pschilkdev/QuadCopter_PP/PPQCU_RC_REMOTE.X/config.h

/* 
 * File:   config.h
 * Author: Philipp
 *
 * Created on January 2, 2016, 3:40 AM
 */

#ifndef CONFIG_H
#define	CONFIG_H

#ifdef	__cplusplus
extern "C" {
#endif

#include <xc.h>



#ifdef	__cplusplus
}
#endif

#endif	/* CONFIG_H */
