pschilkdev/QuadCopter_PP/PPQCU_CU_MAIN.X/NRF.h

/* 
 * File:   NRF.h
 * Author: Philipp
 *
 * Created on January 2, 2016, 6:30 PM
 */

#ifndef NRF_H
#define	NRF_H

#ifdef	__cplusplus
extern "C" {
#endif
    
#include "SPI.h"
#include "config.h"
#include <xc.h>
#include "IO.h"

// ====== Commands ========
    
#define NRF_CMD__R_REGISTER 0b00000000
#define NRF_CMD__W_REGISTER 0b00100000
#define NRF_CMD__R_RX_PAYLOAD 0b01100000
#define NRF_CMD__W_TX_PAYLOAD 0b10100000
#define NRF_CMD__FLUSH_TX 0b11100001
#define NRF_CMD__FLUSH_RX 0b11100010
#define NRF_CMD__REUSE_TX_PL 0b11100011
#define NRF_CMD__ACTIVATE 0b01010000
#define NRF_CMD__R_RX_PL_WID 0b01100000
#define NRF_CMD__W_ACK_PAYLOAD 0b10101000
#define NRF_CMD__W_TX_PAYLOAD_NO_ACK 0b10110000
#define NRF_CMD__NOP 0b11111111
    
// ====== Registers =======
    
#define NRF_RG__CONFIG 0x00
#define NRF_RG__EN_AA 0x01
#define NRF_RG__EN_RXADDR 0x02
#define NRF_RG__SETUP_AW 0x03
#define NRF_RG__SETUP_RETR 0x04
#define NRF_RG__RF_CH 0x05
#define NRF_RG__RF_SETUP 0x06
#define NRF_RG__STATUS 0x07
#define NRF_RG__OBSERVE_TX 0x08
#define NRF_RG__CD 0x09
#define NRF_RG__RX_ADDR_P0 0x0A
#define NRF_RG__RX_ADDR_P1 0x0B
#define NRF_RG__RX_ADDR_P2 0x0C
#define NRF_RG__RX_ADDR_P3 0x0D
#define NRF_RG__RX_ADDR_P4 0x0E
#define NRF_RG__RX_ADDR_P5 0x0F
#define NRF_RG__TX_ADDR 0x10
#define NRF_RG__RX_PW_P0 0x11
#define NRF_RG__RX_PW_P1 0x12
#define NRF_RG__RX_PW_P2 0x13
#define NRF_RG__RX_PW_P3 0x14
#define NRF_RG__RX_PW_P4 0x15
#define NRF_RG__RX_PW_P5 0x16
#define NRF_RG__FIFO_STATUS 0x17
#define NRF_RG__DYNPD 0x1C
#define NRF_RG__FEATURE 0x1D
    
    void NRF_init(SPI_CHANNEL channel);
    int NRF_cmd(char cmd);
    void NRF_wreg(char Reg,char val);
    int  NRF_rreg(char Reg);
    BOOL NRF_check();
    int NRF_RXBuffer_Length();
    int NRF_RXBuffer(char*);
    void NRF_TXBuffer(char, char*,BOOL);
    
//Values
#define byte3 0b01
#define byte4 0b10
#define bye5  0b11    

#define Mbps1 0b000
#define Mbps2 0b001
#define Kps250 0b100
 
#define n18dbm 0b00
#define n12dbm 0b01
#define n6dbm 0b10
#define n0dbm 0b11
    
//CONFIG
#define MASK_RX_DR FALSE
#define MASK_TX_DS TRUE
#define MASK_MAX_RT TRUE
#define EN_CRC TRUE
#define CRCO FALSE

//EN_AA
#define ENAA_P5 FALSE
#define ENAA_P4 FALSE
#define ENAA_P3 FALSE
#define ENAA_P2 FALSE
#define ENAA_P1 FALSE
#define ENAA_P0 TRUE
    
//EN_RXADDR
#define ERX_P5 FALSE
#define ERX_P4 FALSE
#define ERX_P3 FALSE
#define ERX_P2 FALSE
#define ERX_P1 FALSE
#define ERX_P0 FALSE

//SETUP_AW
#define AW byte3

//SETUP_RETR
//0b0 - 0b1111 = 250us - 4000us
#define ARD 0b0011 
//0-15
#define ARC 5      
   
//RF_CH
#define RF_CH 0b110100
    
//RF_SETUP
#define CONT_WAVE FALSE
#define RF_DR Mbps2
#define PLL_LOCK FALSE
#define RF_PWR n0dbm
      
//RX_PW_P0
#define RX_PW_P0 32
    
    

#define nce_H (IO_wCE = 1)
#define nce_L (IO_wCE = 0)
    
#define ncs_H (IO_wCSN = 1)
#define ncs_L (IO_wCSN = 0)

#define ADDRESS0 0b00101011
#define ADDRESS1 0b00101011
#define ADDRESS2 0b00101011
    
#ifdef	__cplusplus
}
#endif

#endif	/* NRF_H */
