pschilkdev/QuadCopter_PP/PPQCU_CU_MAIN.X/DEBUG.h

/* 
 * File:   DEBUG.h
 * Author: Philipp
 *
 * Created on February 21, 2016, 12:16 PM
 */

#ifdef DEBUG

#ifndef DEBUG_H
#define	DEBUG_H

#ifdef	__cplusplus
extern "C" {
#endif

#define DEBUG_LEVEL 1


#ifdef	__cplusplus
}
#endif

#endif	/* DEBUG_H */

#endif /* DEBUG */
