pschilkdev/QuadCopter_PP/PPQCU_CU_MAIN.X/MPL.h

/* 
 * File:   MPL.h
 * Author: Philipp
 *
 * Created on February 6, 2016, 12:12 PM
 */

#ifndef MPL_H
#define	MPL_H

#ifdef	__cplusplus
extern "C" {
#endif

#define IIC_ADR_MPL 0x60

#ifdef	__cplusplus
}
#endif

#endif	/* MPL_H */
