pschilkdev/QuadCopter_PP/PPQCU_CU_MAIN.X/BMI.c

#include "BMI.h"
SPI_CHANNEL spic;

char data[12];

void BMI_init(SPI_CHANNEL spi) {
    spic = spi;

    SPI_init(spic,
            SPI_INITF_MASTER |
            SPI_INITF_MODE_8 |
            SPI_INITF_CKE_ACTIVE_TO_IDLE
            , 9600);

    bcsb_H;
    __asm__("nop");
    __asm__("nop");
}

char BMI_trans(char operation, char address, char value) {
    bcsb_L;
    SPI_trans(spic, (operation << 7) | address);
    volatile char val = SPI_trans(spic, value);
    bcsb_H;
    return val;
}

void BMI_read_multiple(char address, char value[], char num) {
    bcsb_L;
    int i;
    SPI_trans(spic, (BMI_READ << 7) | (address & 0b1111111));
    for (i = 1; i <= num; i++) {
        value[i] = SPI_trans(spic, value[i]);
    }
    bcsb_H;
}

char BMI_read(char address) {
    return BMI_trans(BMI_READ & 0b1, address & 0b1111111, 0x0);
}

void BMI_write(char address, char val) {
    BMI_trans(BMI_WRITE & 0b1, address & 0b1111111, val);
}

void BMI_read_VAL(){
   BMI_read_multiple(BMI_REG__DATA_19,data,11);
}

int BMI_read_GYR_X(){
    return (data[10]<<8)|data[11];
}

int BMI_read_GYR_Y(){
    return (data[8]<<8)|data[9];
}

int BMI_read_GYR_Z(){
    return (data[6]<<8)|data[7];
}
int BMI_read_ACC_X(){
    return (data[4]<<8)|data[5];
}

int BMI_read_ACC_Y(){
    return (data[2]<<8)|data[3];
}

int BMI_read_ACC_Z(){
    return (data[0]<<8)|data[1];
}
